Tinkerforge/humidity-v2-bricklet/software/examples/uc/example_callback.c

// This example is not self-contained.
// It requires usage of the example driver specific to your platform.
// See the HAL documentation.

#include "src/bindings/hal_common.h"
#include "src/bindings/bricklet_humidity_v2.h"

void check(int rc, const char *msg);
void example_setup(TF_HAL *hal);
void example_loop(TF_HAL *hal);

// Callback function for humidity callback
static void humidity_handler(TF_HumidityV2 *device, uint16_t humidity, void *user_data) {
	(void)device; (void)user_data; // avoid unused parameter warning

	tf_hal_printf("Humidity: %d 1/%d %%RH\n", humidity, 100);
}

static TF_HumidityV2 h;

void example_setup(TF_HAL *hal) {
	// Create device object
	check(tf_humidity_v2_create(&h, NULL, hal), "create device object");

	// Register humidity callback to function humidity_handler
	tf_humidity_v2_register_humidity_callback(&h,
	                                          humidity_handler,
	                                          NULL);

	// Set period for humidity callback to 1s (1000ms) without a threshold
	tf_humidity_v2_set_humidity_callback_configuration(&h, 1000, false, 'x', 0, 0);
}

void example_loop(TF_HAL *hal) {
	// Poll for callbacks
	tf_hal_callback_tick(hal, 0);
}
